nokia/miniaturized-environmental-tracker/gecko-fw/peripheral/datalogger/gatekeeper/blank/config/custom_board.h

/**
 * Copyright (c) 2014 - 2017, Nordic Semiconductor ASA
 * 
 * All rights reserved.
 * 
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
 * 3. Neither the name of Nordic Semiconductor ASA nor the names of its
 *    contributors may be used to endorse or promote products derived from this
 *    software without specific prior written permission.
 * 
 * 4. This software, with or without modification, must only be used with a
 *    Nordic Semiconductor ASA integrated circuit.
 * 
 * 5. Any software provided in binary form under this license must not be reverse
 *    engineered, decompiled, modified and/or disassembled.
 * 
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
 */
#ifndef CUSTOM_BOARD_H
#define CUSTOM_BOARD_H

#ifdef __cplusplus
extern "C" {
#endif

#include "nrf_gpio.h"
#define NRF_NUM_GPIO_PINS        32

#define OSC_XL1                  0
#define OSC_XL2                  1
#define ANA_DIG0                 2
#define ANA_DIG1                 3
#define ANA_DIG2                 4
#define ANA_DIG3                 5
#define DIG4                     6
#define TWI_SDA                  7
#define TWI_SCL                  8
#define SPI_MOSI                 9
#define SPI_MISO                 10
#define SPI_SCK                  11
#define IMU_INT1                 12
#define IMU_INT2                 13
#define TWI_SDA_EXT              14
#define TWI_SCL_EXT              15
#define VBAT_OK                  16
#define DIG5                     17
#define PRES_INT                 18
#define SWITCH_CTRL              19
#define CS_MEM                   20
#define RESET                    21
#define COLOUR_INT               22
#define CS_SD                    23
#define MIC_PWR_CTRL             24
#define MIC_DOUT                 25
#define MIC_CLK                  26
#define BAT_MON_EN               27
#define BATTERY                  28
#define LED_G                    29
#define LED_B                    30
#define LED_R                    31

// LEDs definitions for CUSTOM_BOARD
#define LEDS_NUMBER    3

#define LED_START      29
#define LED_1          29
#define LED_2          30
#define LED_3          31
#define LED_STOP       31
#define LED_GREEN      0
#define LED_BLUE       1
#define LED_RED        2

#define LEDS_ACTIVE_STATE 0

#define LEDS_INV_MASK  LEDS_MASK

#define LEDS_LIST { LED_1, LED_2, LED_3 }

#define BSP_LED_0      LED_1
#define BSP_LED_1      LED_2
#define BSP_LED_2      LED_3

#define BUTTONS_NUMBER 0

#define RX_PIN_NUMBER  8
#define TX_PIN_NUMBER  6
#define CTS_PIN_NUMBER 7
#define RTS_PIN_NUMBER 5
#define HWFC           true

#define SPIS_MISO_PIN   28  // SPI MISO signal.
#define SPIS_CSN_PIN    12  // SPI CSN signal.
#define SPIS_MOSI_PIN   25  // SPI MOSI signal.
#define SPIS_SCK_PIN    29  // SPI SCK signal.

#define SPIM0_SCK_PIN   29  // SPI clock GPIO pin number.
#define SPIM0_MOSI_PIN  25  // SPI Master Out Slave In GPIO pin number.
#define SPIM0_MISO_PIN  28  // SPI Master In Slave Out GPIO pin number.
#define SPIM0_SS_PIN    12  // SPI Slave Select GPIO pin number.

#define SPIM1_SCK_PIN   2   // SPI clock GPIO pin number.
#define SPIM1_MOSI_PIN  3   // SPI Master Out Slave In GPIO pin number.
#define SPIM1_MISO_PIN  4   // SPI Master In Slave Out GPIO pin number.
#define SPIM1_SS_PIN    5   // SPI Slave Select GPIO pin number.

#define SPIM2_SCK_PIN   12  // SPI clock GPIO pin number.
#define SPIM2_MOSI_PIN  13  // SPI Master Out Slave In GPIO pin number.
#define SPIM2_MISO_PIN  14  // SPI Master In Slave Out GPIO pin number.
#define SPIM2_SS_PIN    15  // SPI Slave Select GPIO pin number.

// serialization APPLICATION board - temp. setup for running serialized MEMU tests
#define SER_APP_RX_PIN              23    // UART RX pin number.
#define SER_APP_TX_PIN              24    // UART TX pin number.
#define SER_APP_CTS_PIN             2     // UART Clear To Send pin number.
#define SER_APP_RTS_PIN             25    // UART Request To Send pin number.

#define SER_APP_SPIM0_SCK_PIN       27     // SPI clock GPIO pin number.
#define SER_APP_SPIM0_MOSI_PIN      2      // SPI Master Out Slave In GPIO pin number
#define SER_APP_SPIM0_MISO_PIN      26     // SPI Master In Slave Out GPIO pin number
#define SER_APP_SPIM0_SS_PIN        23     // SPI Slave Select GPIO pin number
#define SER_APP_SPIM0_RDY_PIN       25     // SPI READY GPIO pin number
#define SER_APP_SPIM0_REQ_PIN       24     // SPI REQUEST GPIO pin number

// serialization CONNECTIVITY board
#define SER_CON_RX_PIN              24    // UART RX pin number.
#define SER_CON_TX_PIN              23    // UART TX pin number.
#define SER_CON_CTS_PIN             25    // UART Clear To Send pin number. Not used if HWFC is set to false.
#define SER_CON_RTS_PIN             2     // UART Request To Send pin number. Not used if HWFC is set to false.


#define SER_CON_SPIS_SCK_PIN        27    // SPI SCK signal.
#define SER_CON_SPIS_MOSI_PIN       2     // SPI MOSI signal.
#define SER_CON_SPIS_MISO_PIN       26    // SPI MISO signal.
#define SER_CON_SPIS_CSN_PIN        23    // SPI CSN signal.
#define SER_CON_SPIS_RDY_PIN        25    // SPI READY GPIO pin number.
#define SER_CON_SPIS_REQ_PIN        24    // SPI REQUEST GPIO pin number.

#define SER_CONN_CHIP_RESET_PIN     11    // Pin used to reset connectivity chip

// I2S Pins (dummy as we don't know where they are!)
#define PWM_I2S_SCK_PIN             13
#define PWM_I2S_WS_PIN              13

// I2C Pins
#define SCL_PIN                     8
#define SDA_PIN                     7

#define BATT_VOLTAGE_DIVIDER_R1      1500000
#define BATT_VOLTAGE_DIVIDER_R2      180000

// Low frequency clock source to be used by the SoftDevice
#define NRF_CLOCK_LFCLKSRC      {.source        = NRF_CLOCK_LF_SRC_XTAL,            \
                                 .rc_ctiv       = 0,                                \
                                 .rc_temp_ctiv  = 0,                                \
                                 .xtal_accuracy = NRF_CLOCK_LF_XTAL_ACCURACY_20_PPM}

#ifdef __cplusplus
}
#endif

#endif // CUSTOM_BOARD_H
